lintec-unt/voice-controlled-hospital-bed/PCB/PCB3dVIew.jpg

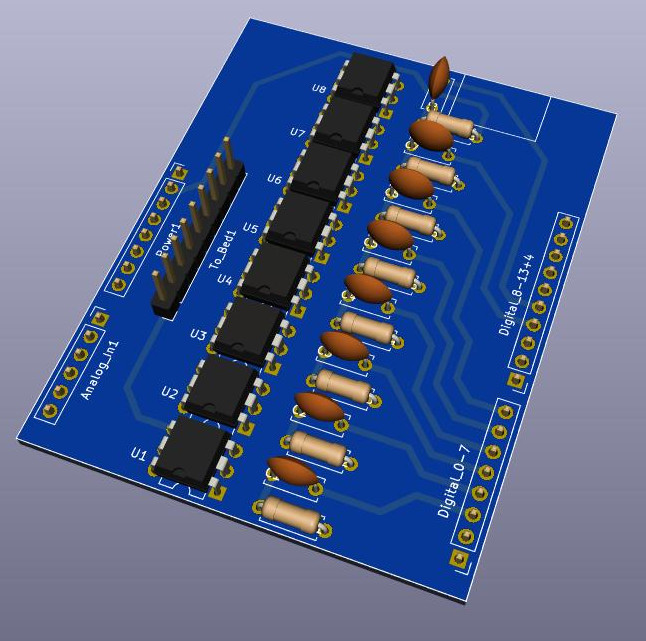
PCB/PCB3dVIew.jpg
