lintec-unt/voice-controlled-hospital-bed/PCSoftwareCode/Resources/az_cbz_aba1.JPG

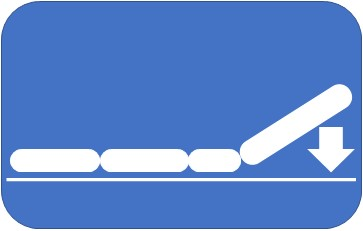
PCSoftwareCode/Resources/az_cbz_aba1.JPG
