lintec-unt/voice-controlled-hospital-bed/PCSoftwareCode/Resources/az_pen_ad1.JPG

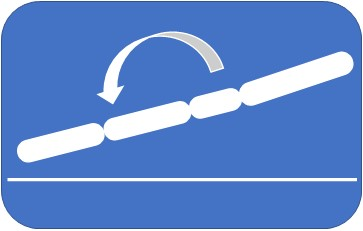
PCSoftwareCode/Resources/az_pen_ad1.JPG
