lintec-unt/voice-controlled-hospital-bed/PCSoftwareCode/Resources/az_pen_at1.JPG

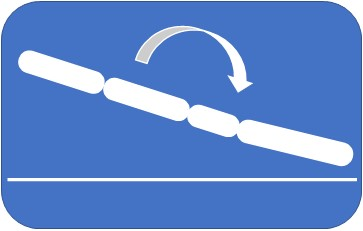
PCSoftwareCode/Resources/az_pen_at1.JPG
