lintec-unt/voice-controlled-hospital-bed/PCSoftwareCode/Resources/az_reposo1.JPG

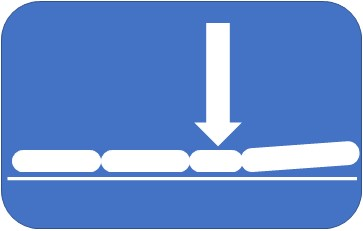
PCSoftwareCode/Resources/az_reposo1.JPG
