lintec-unt/voice-controlled-hospital-bed/PCSoftwareCode/Resources/FondoModificado_01.gif

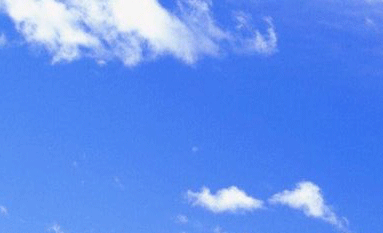
PCSoftwareCode/Resources/FondoModificado_01.gif
