lintec-unt/voice-controlled-hospital-bed/PCSoftwareCode/Resources/FondoModificado_05.gif

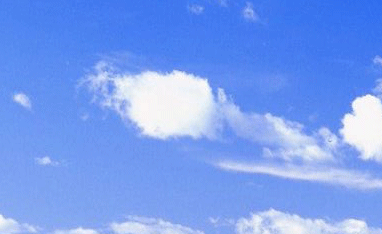
PCSoftwareCode/Resources/FondoModificado_05.gif
