lintec-unt/voice-controlled-hospital-bed/PCSoftwareCode/Resources/FondoModificado_06.gif

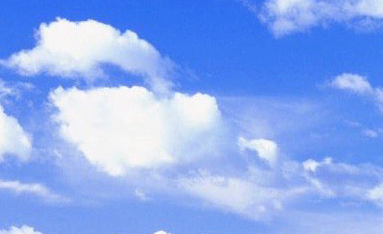
PCSoftwareCode/Resources/FondoModificado_06.gif
