lintec-unt/voice-controlled-hospital-bed/PCSoftwareCode/Resources/FondoModificado_07.gif

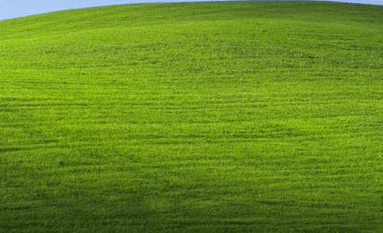
PCSoftwareCode/Resources/FondoModificado_07.gif
