lintec-unt/voice-controlled-hospital-bed/PCSoftwareCode/Resources/FondoModificado_08.gif

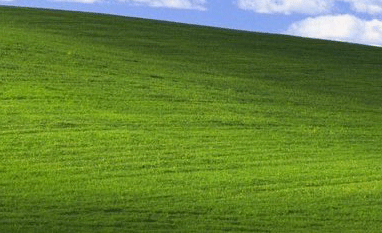
PCSoftwareCode/Resources/FondoModificado_08.gif
