lintec-unt/voice-controlled-hospital-bed/PCSoftwareCode/Resources/FondoModificado_09.gif

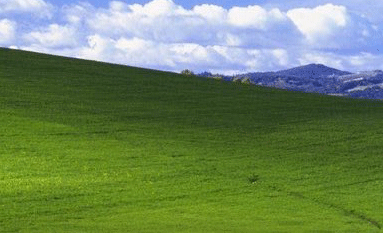
PCSoftwareCode/Resources/FondoModificado_09.gif
