lintec-unt/voice-controlled-hospital-bed/PCSoftwareCode/Resources/FondoModificado_099.gif

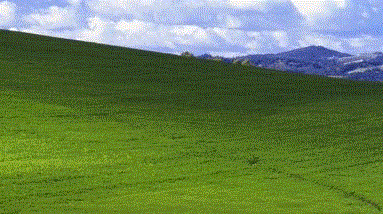
PCSoftwareCode/Resources/FondoModificado_099.gif
