lintec-unt/voice-controlled-hospital-bed/PCSoftwareCode/Resources/FondoModificado_0888.gif

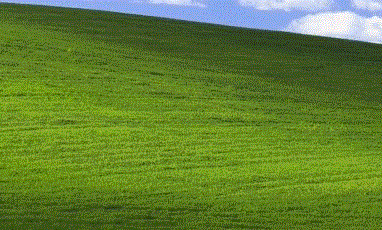
PCSoftwareCode/Resources/FondoModificado_0888.gif
