lintec-unt/voice-controlled-hospital-bed/PCSoftwareCode/Resources/images.png

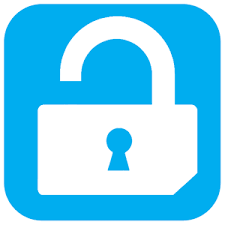
PCSoftwareCode/Resources/images.png
