lintec-unt/voice-controlled-hospital-bed/PCSoftwareCode/Resources/locked1.png

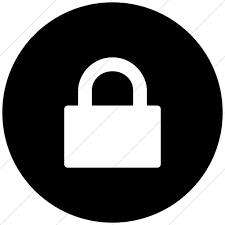
PCSoftwareCode/Resources/locked1.png
