lintec-unt/voice-controlled-hospital-bed/PCSoftwareCode/Resources/unlock_white.png

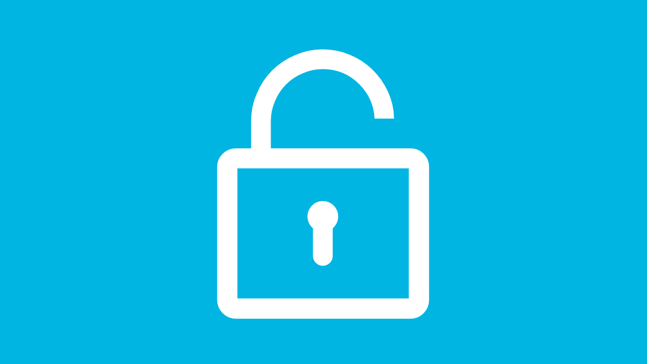
PCSoftwareCode/Resources/unlock_white.png
