lintec-unt/voice-controlled-hospital-bed/PCSoftwareCode/window.png

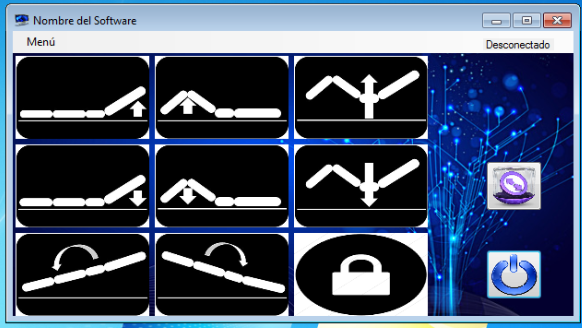
PCSoftwareCode/window.png
