lintec-unt/voice-controlled-hospital-bed/STLCase/snapCase.png

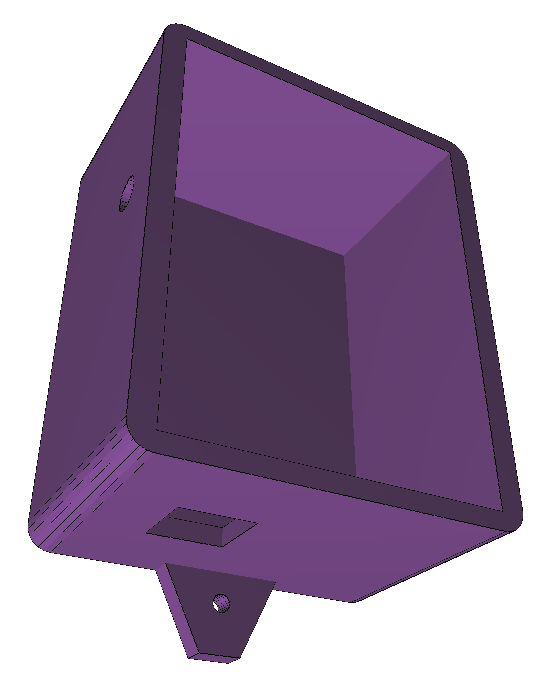
STLCase/snapCase.png
